jswans33/James-openflight/cad/IARC_case/step/OPS_mount.step

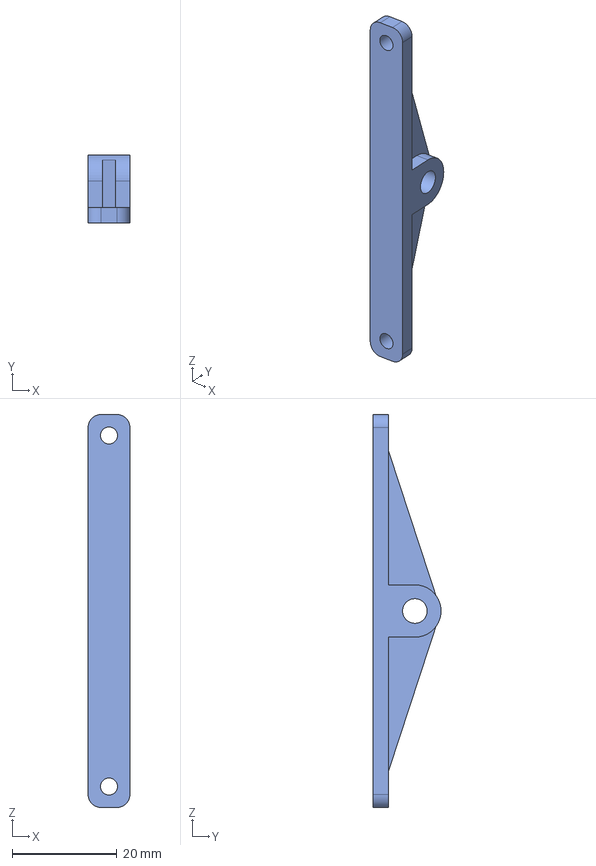
[picture p39: CAD file, 2026-06-16]
cad/IARC_case/step/OPS_mount.step
8.00 x 13.0 x 75.0 mm
