jswans33/James-openflight/cad/IARC_case/step/curvy_backplate.step

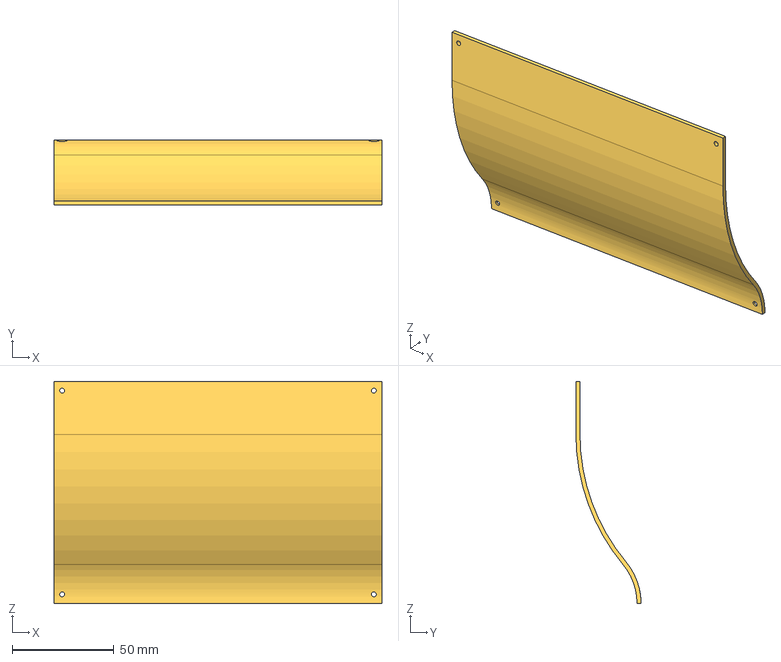
[picture p40: CAD file, 2026-06-16]
cad/IARC_case/step/curvy_backplate.step
161.0 x 32.0 x 109.0 mm
