jswans33/James-openflight/cad/IARC_case/step/monitor_back.step

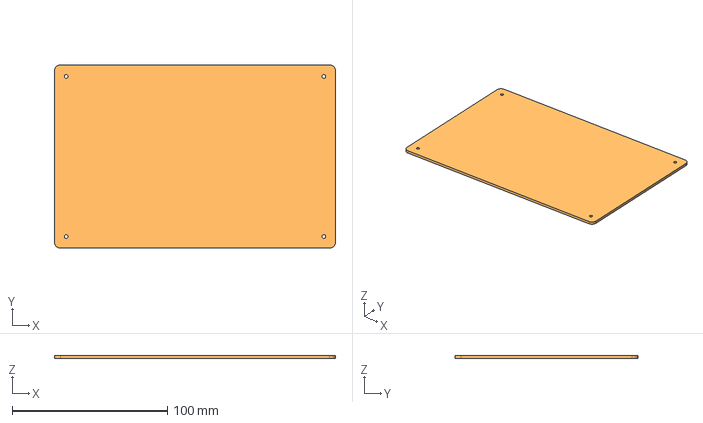
[picture p41: CAD file, 2026-06-16]
cad/IARC_case/step/monitor_back.step
181.0 x 118.0 x 2.00 mm
