jswans33/James-openflight/cad/IARC_case/step/monitor_mount.step

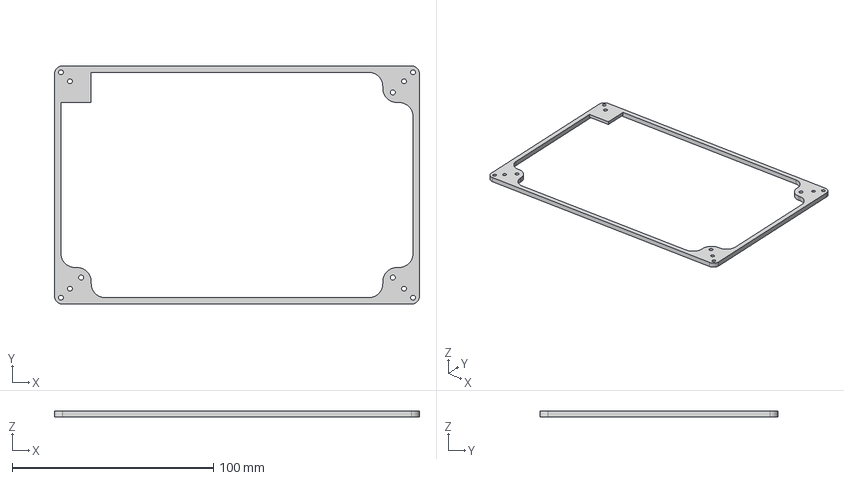
[picture p42: CAD file, 2026-06-16]
cad/IARC_case/step/monitor_mount.step
181.4 x 118.4 x 3.00 mm
