jswans33/James-openflight/cad/IARC_case/step/name_plate.step

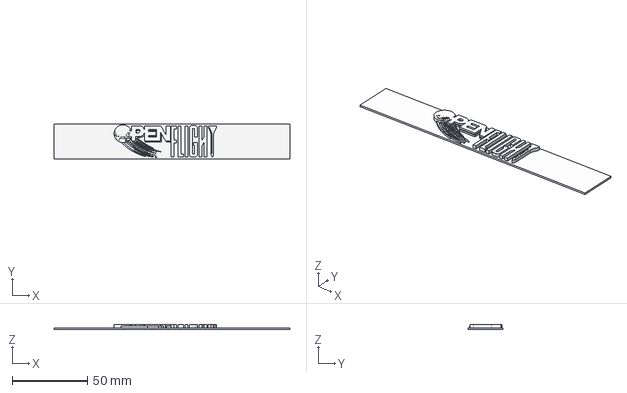
[picture p43: CAD file, 2026-06-16]
cad/IARC_case/step/name_plate.step
156.6 x 23.2 x 3.00 mm
