jswans33/James-openflight/cad/IARC_case/step/KLD7_h_mount_R_v2.step

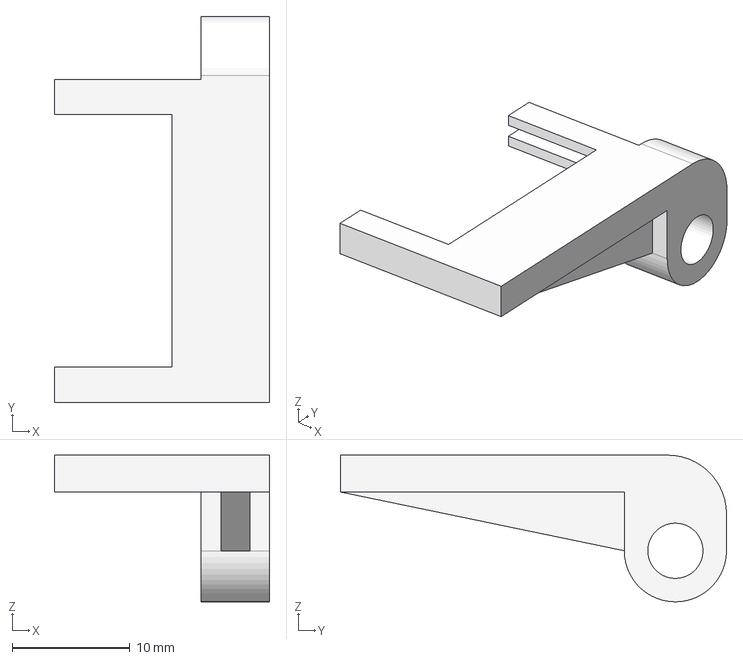
[picture p44: CAD file, 2026-06-16]
cad/IARC_case/step/KLD7_h_mount_R_v2.step
18.3 x 32.8 x 12.5 mm
