jswans33/James-openflight/src/openflight/rolling_buffer/trigger.py

"""
Trigger strategies for rolling buffer capture.

Defines different methods for determining when to capture the rolling buffer.
"""

import logging
import time
from abc import ABC, abstractmethod
from datetime import datetime, timezone
from typing import TYPE_CHECKING, List, Optional

from .processor import RollingBufferProcessor
from .types import IQCapture

if TYPE_CHECKING:
    from ..ops243 import OPS243Radar

# Incremented per capture for log sequencing (not shot number)

logger = logging.getLogger("openflight.rolling_buffer.trigger")


class TriggerStrategy(ABC):
    """
    Base class for trigger strategies.

    A trigger strategy determines when to capture the rolling buffer.
    Different strategies trade off between simplicity, reliability, and efficiency.
    """

    MIN_VALID_OUTBOUND_MPH = 15.0

    def __init__(self, pre_trigger_segments: int = 12):
        self._diagnostics: List[dict] = []
        self.pre_trigger_segments = pre_trigger_segments

    def drain_diagnostics(self) -> List[dict]:
        """Return and clear accumulated diagnostic entries.

        Diagnostics are accumulated during wait_for_trigger() calls.
        The monitor drains these after each call to log and emit them.
        """
        diagnostics = self._diagnostics
        self._diagnostics = []
        return diagnostics

    def _append_diagnostic(
        self,
        accepted: bool,
        reason: str,
        response_bytes: int = 0,
        total_readings: int = 0,
        outbound_readings: int = 0,
        inbound_readings: int = 0,
        peak_outbound_mph: float = 0.0,
        peak_inbound_mph: float = 0.0,
        all_outbound_speeds: Optional[List[float]] = None,
        all_inbound_speeds: Optional[List[float]] = None,
        peak_outbound_magnitude: float = 0.0,
        peak_inbound_magnitude: float = 0.0,
        trigger_latency_ms: Optional[float] = None,
    ):
        """Append a diagnostic entry for the current trigger event."""
        entry = {
            "timestamp": datetime.now(timezone.utc).isoformat(),
            "accepted": accepted,
            "reason": reason,
            "response_bytes": response_bytes,
            "total_readings": total_readings,
            "outbound_readings": outbound_readings,
            "inbound_readings": inbound_readings,
            "peak_outbound_mph": peak_outbound_mph,
            "peak_inbound_mph": peak_inbound_mph,
            "all_outbound_speeds": all_outbound_speeds or [],
            "all_inbound_speeds": all_inbound_speeds or [],
            "peak_outbound_magnitude": peak_outbound_magnitude,
            "peak_inbound_magnitude": peak_inbound_magnitude,
        }
        if trigger_latency_ms is not None:
            entry["trigger_latency_ms"] = trigger_latency_ms
        self._diagnostics.append(entry)

    def _summarize_capture_activity(
        self,
        processor: RollingBufferProcessor,
        capture: IQCapture,
    ) -> dict:
        """Summarize movement in a capture before accepting a sound trigger."""
        timeline = processor.process_standard(capture)
        all_readings = timeline.readings
        all_outbound = [r for r in all_readings if r.is_outbound]
        all_inbound = [r for r in all_readings if not r.is_outbound]
        outbound_speeds = [r.speed_mph for r in all_outbound]
        inbound_speeds = [r.speed_mph for r in all_inbound]
        valid_outbound = [r for r in all_outbound if r.speed_mph >= self.MIN_VALID_OUTBOUND_MPH]

        return {
            "total_readings": len(all_readings),
            "outbound_readings": len(all_outbound),
            "inbound_readings": len(all_inbound),
            "peak_outbound_mph": max(outbound_speeds, default=0),
            "peak_inbound_mph": max(inbound_speeds, default=0),
            "all_outbound_speeds": outbound_speeds,
            "all_inbound_speeds": inbound_speeds,
            "peak_outbound_magnitude": max((r.magnitude for r in all_outbound), default=0),
            "peak_inbound_magnitude": max((r.magnitude for r in all_inbound), default=0),
            "valid_outbound_count": len(valid_outbound),
            "valid_peak_outbound_mph": max(
                (r.speed_mph for r in valid_outbound),
                default=0,
            ),
        }

    def _append_activity_diagnostic(
        self,
        summary: dict,
        *,
        accepted: bool,
        reason: str,
        response_bytes: int,
        trigger_latency_ms: Optional[float] = None,
    ):
        """Append a diagnostic entry using capture-activity summary fields."""
        self._append_diagnostic(
            accepted=accepted,
            reason=reason,
            response_bytes=response_bytes,
            total_readings=summary["total_readings"],
            outbound_readings=summary["outbound_readings"],
            inbound_readings=summary["inbound_readings"],
            peak_outbound_mph=summary["peak_outbound_mph"],
            peak_inbound_mph=summary["peak_inbound_mph"],
            all_outbound_speeds=summary["all_outbound_speeds"],
            all_inbound_speeds=summary["all_inbound_speeds"],
            peak_outbound_magnitude=summary["peak_outbound_magnitude"],
            peak_inbound_magnitude=summary["peak_inbound_magnitude"],
            trigger_latency_ms=trigger_latency_ms,
        )

    @abstractmethod
    def wait_for_trigger(
        self,
        radar: "OPS243Radar",
        processor: RollingBufferProcessor,
        timeout: float = 30.0,
    ) -> Optional[IQCapture]:
        """
        Wait for trigger condition and capture buffer.

        Args:
            radar: Connected OPS243Radar instance in rolling buffer mode
            processor: Processor for parsing capture response
            timeout: Maximum time to wait for trigger

        Returns:
            IQCapture if triggered and captured, None if timeout or error
        """
        pass

    @abstractmethod
    def reset(self):
        """Reset trigger state for next capture."""
        pass
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
