jswans33/James-openflight/src/openflight/rolling_buffer/types.py

"""
Data types for rolling buffer mode.

These types represent the raw I/Q data captured from the radar,
the processed speed timeline, and spin detection results.
"""

from dataclasses import dataclass, field
from datetime import datetime
from typing import List, Optional


@dataclass
class IQCapture:
    """
    Raw I/Q data captured from S! command in rolling buffer mode.

    The radar returns 4096 samples each for I (in-phase) and Q (quadrature)
    components of the Doppler signal. At 30ksps, this represents ~136ms of data.

    Attributes:
        sample_time: Radar timestamp when sampling started (seconds since power-on)
        trigger_time: Radar timestamp when trigger fired
        i_samples: 4096 in-phase samples (raw ADC values, 0-4095)
        q_samples: 4096 quadrature samples (raw ADC values, 0-4095)
        timestamp: Python timestamp when capture was received
        first_byte_timestamp: Host epoch timestamp when the first byte of a
            hardware-triggered capture arrived from the radar.
        trigger_timestamp: Host epoch timestamp when the hardware trigger fired,
            derived from first_byte_timestamp and the post-trigger buffer span.
    """

    sample_time: float
    trigger_time: float
    i_samples: List[int]
    q_samples: List[int]
    timestamp: float = field(default_factory=lambda: datetime.now().timestamp())
    first_byte_timestamp: Optional[float] = None
    trigger_timestamp: Optional[float] = None
    trigger_timestamp_source: Optional[str] = None
    clock_sync_offset_s: Optional[float] = None

    def __post_init__(self) -> None:
        """Infer the hardware trigger epoch when first-byte timing is available."""
        if self.trigger_timestamp is None:
            self.apply_trigger_timestamp_from_first_byte()

    @property
    def num_samples(self) -> int:
        """Total number of I/Q sample pairs."""
        return len(self.i_samples)

    @property
    def duration_ms(self) -> float:
        """Duration of capture in milliseconds (at 30ksps)."""
        return (self.num_samples / 30000) * 1000

    @property
    def trigger_offset_ms(self) -> float:
        """Time offset of trigger from start of buffer in milliseconds."""
        return (self.trigger_time - self.sample_time) * 1000

    @property
    def post_trigger_duration_ms(self) -> float:
        """Duration of capture sampled after the hardware trigger."""
        return min(
            max(self.duration_ms - self.trigger_offset_ms, 0.0),
            self.duration_ms,
        )

    def infer_trigger_timestamp_from_first_byte(self) -> Optional[float]:
        """Return hardware trigger epoch inferred from first response byte time."""
        if self.first_byte_timestamp is None:
            return None
        return self.first_byte_timestamp - self.post_trigger_duration_ms / 1000.0
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
